nickbild/vectron_vga_plus/media/20211205_120411.jpg

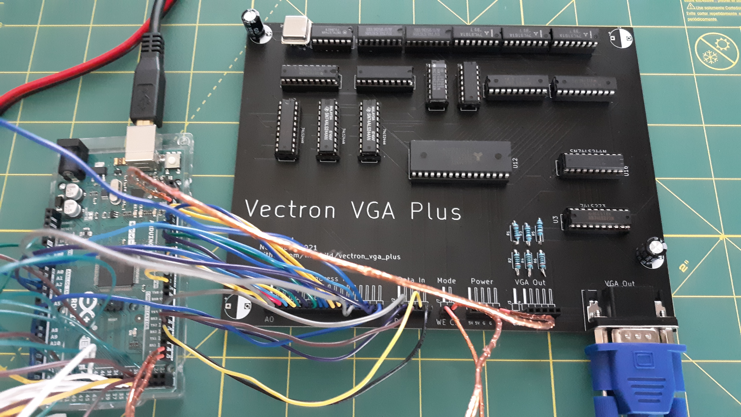
media/20211205_120411.jpg
