nickbild/vectron_vga_plus/vectron_vga_plus_arduino_tester/vectron_vga_plus_arduino_tester.ino

#define ADDR0 2
#define ADDR1 3
#define ADDR2 4
#define ADDR3 5
#define ADDR4 6
#define ADDR5 7
#define ADDR6 8
#define ADDR7 9
#define ADDR8 10
#define ADDR9 11
#define ADDR10 12
#define ADDR11 13
#define ADDR12 A0
#define ADDR13 A1
#define ADDR14 A2
#define ADDR15 A3
#define ADDR16 A4
#define ADDR17 A15

#define DATA0 14
#define DATA1 15
#define DATA2 16
#define DATA3 17
#define DATA4 18

#define WE 20
#define CE 21

#define FP 8       // 8
#define BP 24      // 24
#define HS 48      // 48

uint32_t address = 0;

void setup() {
  Serial.begin(115200);

  pinMode(ADDR0, OUTPUT);
  pinMode(ADDR1, OUTPUT);
  pinMode(ADDR2, OUTPUT);
  pinMode(ADDR3, OUTPUT);
  pinMode(ADDR4, OUTPUT);
  pinMode(ADDR5, OUTPUT);
  pinMode(ADDR6, OUTPUT);
  pinMode(ADDR7, OUTPUT);
  pinMode(ADDR8, OUTPUT);
  pinMode(ADDR9, OUTPUT);
  pinMode(ADDR10, OUTPUT);
  pinMode(ADDR11, OUTPUT);
  pinMode(ADDR12, OUTPUT);
  pinMode(ADDR13, OUTPUT);
  pinMode(ADDR14, OUTPUT);
  pinMode(ADDR15, OUTPUT);
  pinMode(ADDR16, OUTPUT);
  pinMode(ADDR17, OUTPUT);

  pinMode(DATA0, OUTPUT);
  pinMode(DATA1, OUTPUT);
  pinMode(DATA2, OUTPUT);
  pinMode(DATA3, OUTPUT);
  pinMode(DATA4, OUTPUT);

  pinMode(WE, OUTPUT);
  pinMode(CE, OUTPUT);

  // Initial chip state.
  digitalWrite(WE, 1);
  digitalWrite(CE, 1);
}

void loop() {
  Serial.println("Clearing RAM.");
  for (uint32_t v = 0; v < 210000; v++) {
    writeSRAM(v, 31);
  }

  Serial.println("Starting write.");

  // Vertical visible.
//  displayVisibleRowRed();
//  displayVisibleRowRed();
  for (uint16_t row = 0; row < 480; row++) {
    displayVisibleRow();
  }
//  displayVisibleRowRed();

  // Vertical front porch.
  for (uint8_t row = 0; row < 9; row++) { // 9
    displayInvisibleRow();
  }

  // Vertical Sync.
  //  displayVerticalSyncRow();
  displayVerticalSyncRows();

  // Vertical back porch.
  for (uint8_t row = 0; row < 53; row++) { // 33
    displayInvisibleRow();
  }




plotPixel(14, 42, 25);
plotPixel(15, 42, 25);
plotPixel(16, 42, 25);
plotPixel(17, 42, 25);
plotPixel(18, 42, 25);
plotPixel(20, 42, 25);
plotPixel(21, 42, 25);
plotPixel(22, 42, 25);
plotPixel(23, 42, 25);
plotPixel(31, 42, 25);
plotPixel(32, 42, 25);
plotPixel(33, 42, 25);
plotPixel(34, 42, 25);
plotPixel(35, 42, 25);
plotPixel(36, 42, 25);
plotPixel(37, 42, 25);
plotPixel(38, 42, 25);
plotPixel(39, 42, 25);
plotPixel(40, 42, 25);
plotPixel(41, 42, 25);
plotPixel(42, 42, 25);
plotPixel(43, 42, 25);
plotPixel(44, 42, 25);
plotPixel(45, 42, 25);
plotPixel(54, 42, 25);
plotPixel(55, 42, 25);
plotPixel(56, 42, 25);
plotPixel(57, 42, 25);
plotPixel(58, 42, 25);
plotPixel(59, 42, 25);
plotPixel(60, 42, 25);
plotPixel(61, 42, 25);
plotPixel(62, 42, 25);
plotPixel(63, 42, 25);
plotPixel(64, 42, 25);
plotPixel(65, 42, 25);
plotPixel(66, 42, 25);
plotPixel(67, 42, 25);
plotPixel(68, 42, 25);
plotPixel(69, 42, 25);
plotPixel(70, 42, 25);
plotPixel(80, 42, 25);
plotPixel(81, 42, 25);
plotPixel(82, 42, 25);
plotPixel(83, 42, 25);
plotPixel(84, 42, 25);
plotPixel(85, 42, 25);
plotPixel(86, 42, 25);
plotPixel(87, 42, 25);
plotPixel(88, 42, 25);
plotPixel(89, 42, 25);
plotPixel(90, 42, 25);
plotPixel(91, 42, 25);
plotPixel(122, 42, 25);
plotPixel(123, 42, 25);
plotPixel(124, 42, 25);
plotPixel(125, 42, 25);
plotPixel(126, 42, 25);
plotPixel(127, 42, 25);
plotPixel(128, 42, 25);
plotPixel(129, 42, 25);
plotPixel(130, 42, 25);
plotPixel(131, 42, 25);
plotPixel(132, 42, 25);
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
plotPixel(161, 73, 25);
plotPixel(162, 73, 25);
plotPixel(163, 73, 25);
plotPixel(164, 73, 25);
plotPixel(165, 73, 25);
plotPixel(166, 73, 25);
plotPixel(167, 73, 25);
plotPixel(168, 73, 25);
plotPixel(169, 73, 25);
plotPixel(177, 73, 25);
plotPixel(178, 73, 25);
plotPixel(179, 73, 25);
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
